wanbeiyu/research/cstick.kicad_sch

## KiCad design cstick.kicad_sch (2024-03-10)

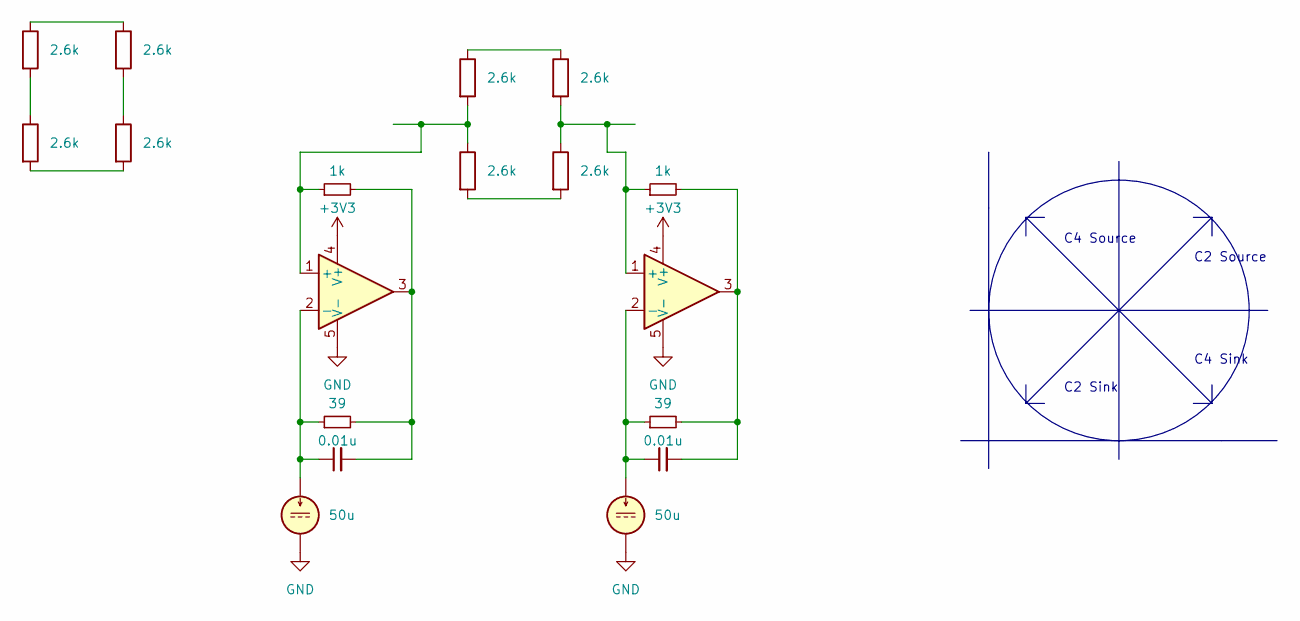
[picture p11: schematic cstick.kicad_sch]

Parts:
C1, C2: 0.01u
I1, I2: 50u
R1, R2, R3, R4, R5, R6, R7, R8: 2.6k
R9, R12: 39
R10, R11: 1k
U1, U2: ${SIM.PARAMS}

Connections:
+3V3: U1.4 (V+), U2.4 (V+)
GND: I1.2, I2.2, U1.5 (V-), U2.5 (V-)
unnamed: C1.1, I1.1, R9.1, U1.2 (-)
unnamed: C1.2, R9.2, R10.2, U1.3
unnamed: C2.1, I2.1, R12.1, U2.2 (-)
unnamed: C2.2, R11.2, R12.2, U2.3
unnamed: R1.1, R3.1
unnamed: R1.2, R2.1
unnamed: R2.2, R4.2
unnamed: R3.2, R4.1
unnamed: R5.1, R7.1
unnamed: R6.2, R8.2
unnamed: R5.2, R6.1, R10.1, U1.1 (+)
unnamed: R7.2, R8.1, R11.1, U2.1 (+)

Notes on the sheet:
C2 Source
C4 Sink
C4 Source
C2 Sink
