wanbeiyu/research/touchscreen.kicad_sch

## KiCad design touchscreen.kicad_sch (2024-03-24)

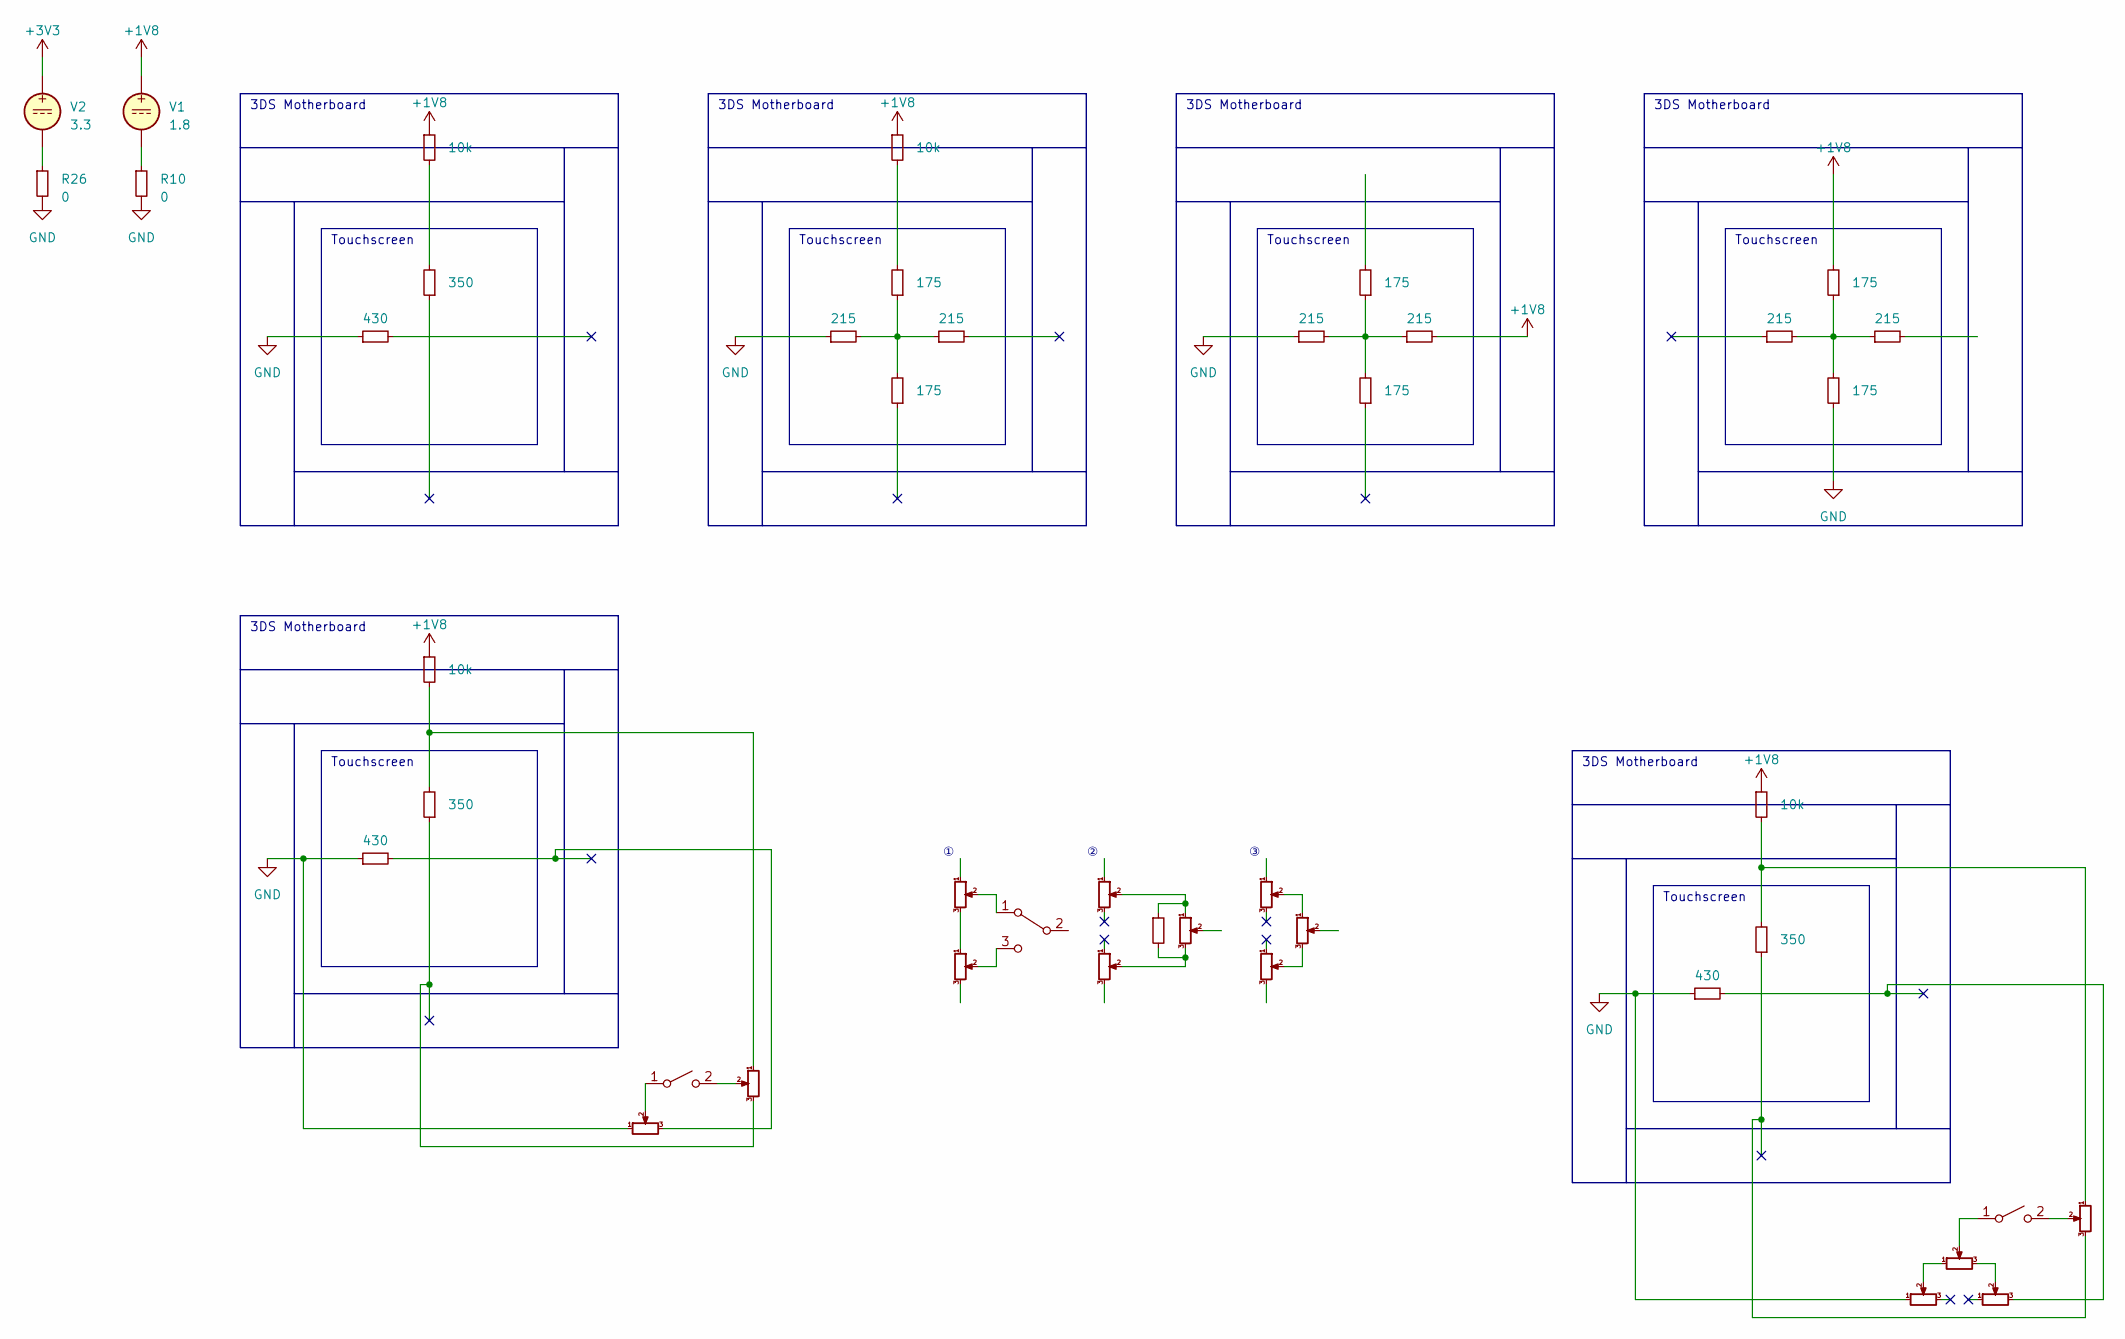
[picture p12: schematic touchscreen.kicad_sch]

Parts:
R1, R2, R7: 430
R3, R5, R8, R12: 10k
R4, R6, R9: 350
R10, R26: 0
R11, R15, R16, R19, R20, R23: 215
R13, R14, R17, R18, R21, R22: 175
R24: 4.7
RV1, RV2, RV3, RV4, RV5, RV6, RV7, RV9, RV10, RV11, RV12, RV13, RV14, RV15: R_Potentiometer_Small
SW1, SW3: 0
SW2: SW_SPDT
V1: 1.8
V2: 3.3

Connections:
+1V8: R3.1, R5.1, R8.1, R12.1, R19.2, R21.2, V1.1
+3V3: V2.1
GND: R1.1, R2.1, R7.1, R10.2, R11.1, R16.1, R22.1, R26.2, RV7.1, RV13.1
unnamed: R2.2, RV7.3
unnamed: R3.2, R4.2
unnamed: R5.2, R6.2, RV6.1
unnamed: R6.1, RV6.3
unnamed: R7.2, RV14.3
unnamed: R8.2, R9.2, RV9.1
unnamed: R9.1, RV9.3
unnamed: R10.1, V1.2
unnamed: R11.2, R13.1, R14.2, R15.1
unnamed: R12.2, R13.2
unnamed: R16.2, R17.1, R18.2, R19.1
unnamed: R20.2, R21.1, R22.2, R23.1
unnamed: R24.1, RV10.2, RV12.1
unnamed: R24.2, RV11.2, RV12.3
unnamed: R26.1, V2.2
unnamed: RV1.2, RV2.1
unnamed: RV2.3, RV3.2
unnamed: RV4.2, SW2.1 (A)
unnamed: RV4.3, RV5.1
unnamed: RV5.2, SW2.3 (C)
unnamed: RV6.2, SW1.2 (B)
unnamed: RV7.2, SW1.1 (A)
unnamed: RV9.2, SW3.2 (B)
unnamed: RV13.2, RV15.1
unnamed: RV14.2, RV15.3
unnamed: RV15.2, SW3.1 (A)

Notes on the sheet:
3DS Motherboard
Touchscreen
